QuantumTechClub/QuanClick/img/check_micro_usb.jpg

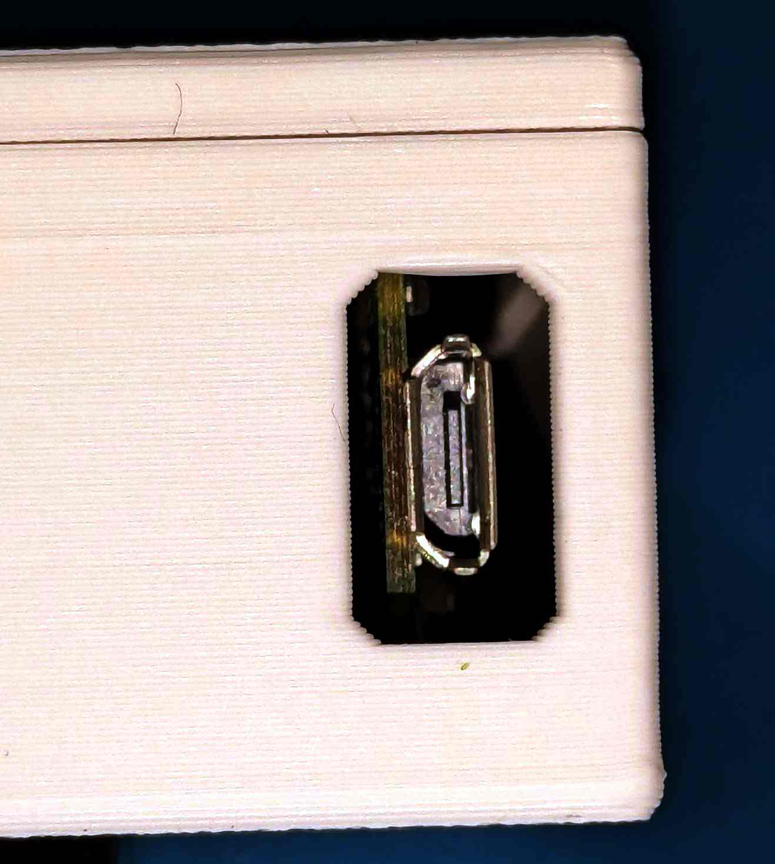
img/check_micro_usb.jpg
