QuantumTechClub/QuanClick/img/insert_pico.jpg

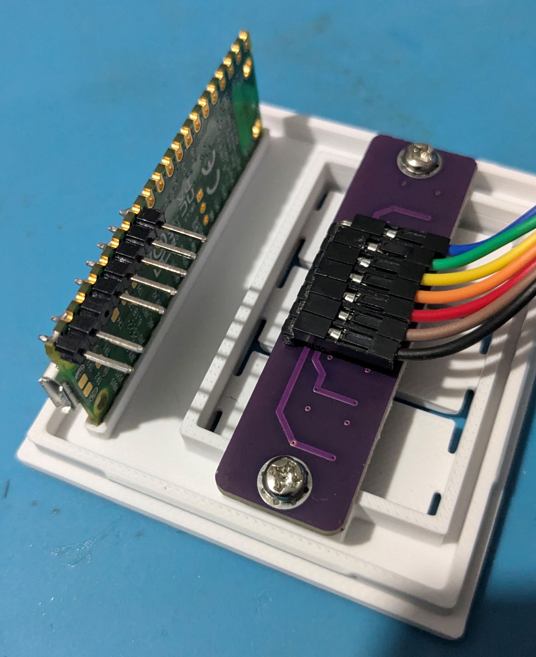
img/insert_pico.jpg
