QuantumTechClub/QuanClick/cad/QuanClick_Num6.stl

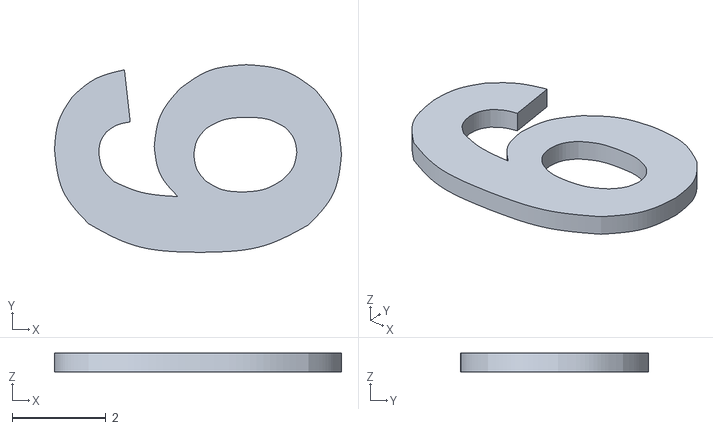
[picture p24: CAD file, 2024-11-24]
cad/QuanClick_Num6.stl
6.13 x 4.01 x 0.4
