QuantumTechClub/QuanClick/cad/QuanClick_LetL.stl

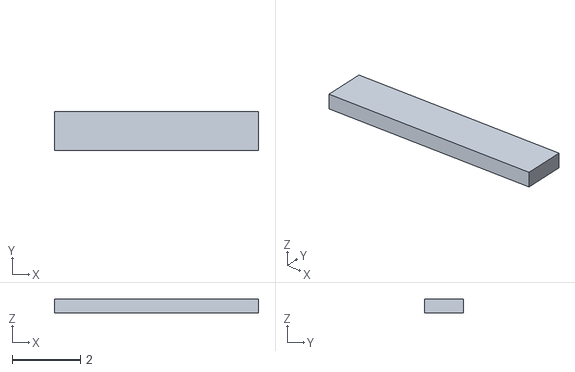
[picture p25: CAD file, 2024-11-24]
cad/QuanClick_LetL.stl
6.00 x 1.15 x 0.4
