QuantumTechClub/QuanClick/cad/QuanClick_LetIdot.stl

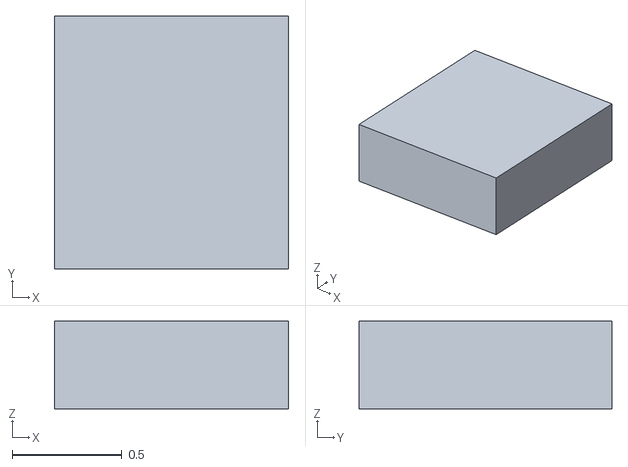
[picture p26: CAD file, 2024-11-24]
cad/QuanClick_LetIdot.stl
1.06 x 1.15 x 0.4
